angelman7/WRO-Binaries/jetson/scripts/images/img_0.png

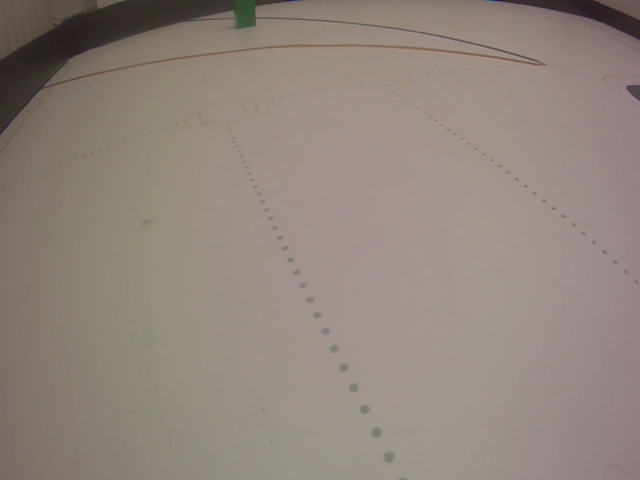
jetson/scripts/images/img_0.png
