angelman7/WRO-Binaries/jetson/scripts/images/img_1.png

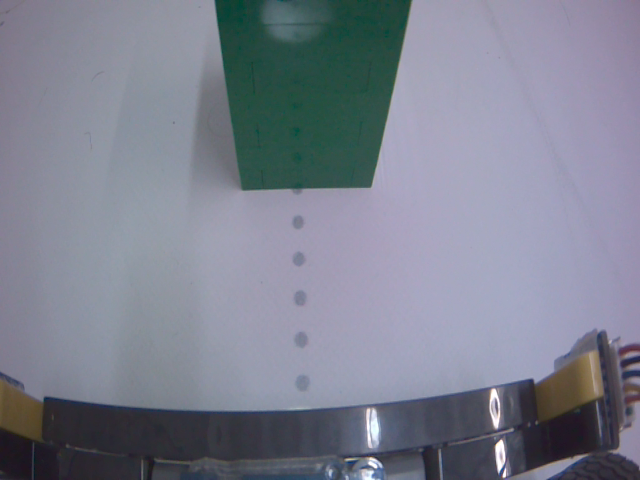
jetson/scripts/images/img_1.png
