angelman7/WRO-Binaries/jetson/scripts/images/img_2.png

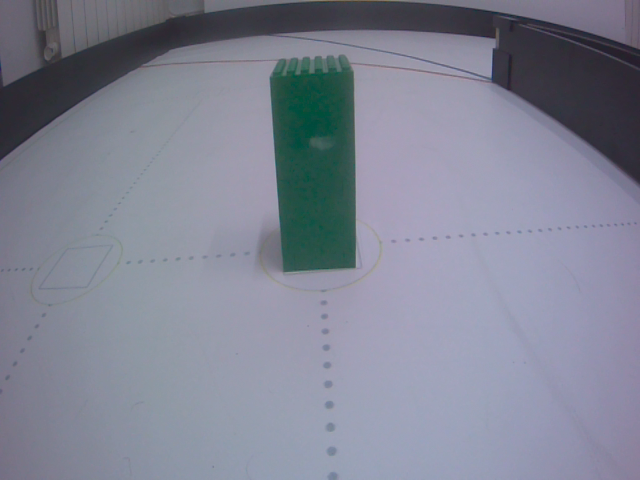
jetson/scripts/images/img_2.png
