angelman7/WRO-Binaries/jetson/scripts/images/img_7.png

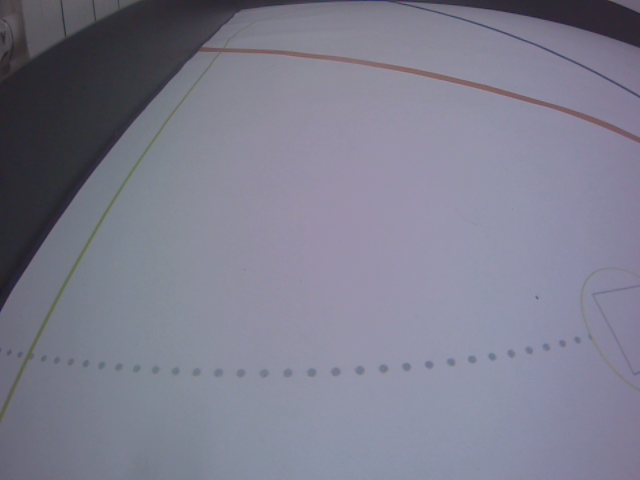
jetson/scripts/images/img_7.png
