angelman7/WRO-Binaries/jetson/scripts/images/img_9.png

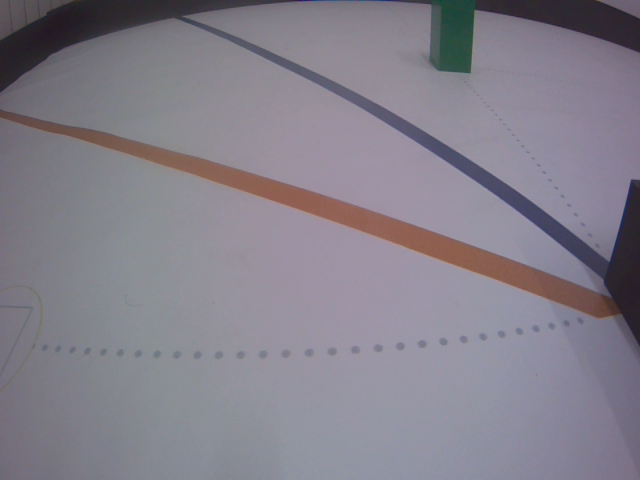
jetson/scripts/images/img_9.png
