angelman7/WRO-Binaries/jetson/scripts/images/img_11.png

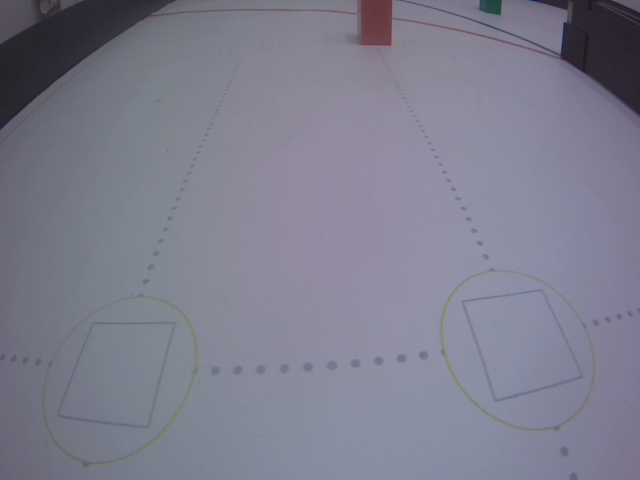
jetson/scripts/images/img_11.png
