angelman7/WRO-Binaries/jetson/scripts/images/img_13.png

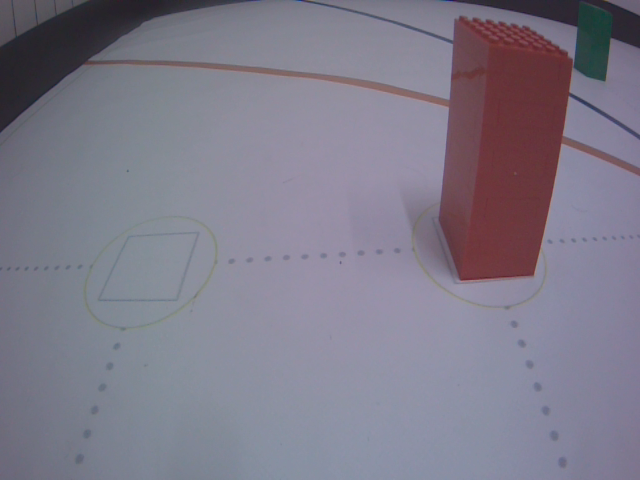
jetson/scripts/images/img_13.png
