angelman7/WRO-Binaries/jetson/scripts/images/img_15.png

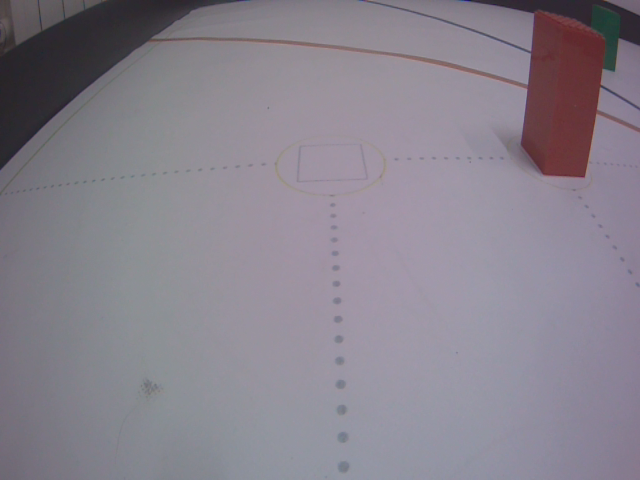
jetson/scripts/images/img_15.png
