angelman7/WRO-Binaries/schemes/Buttons.png

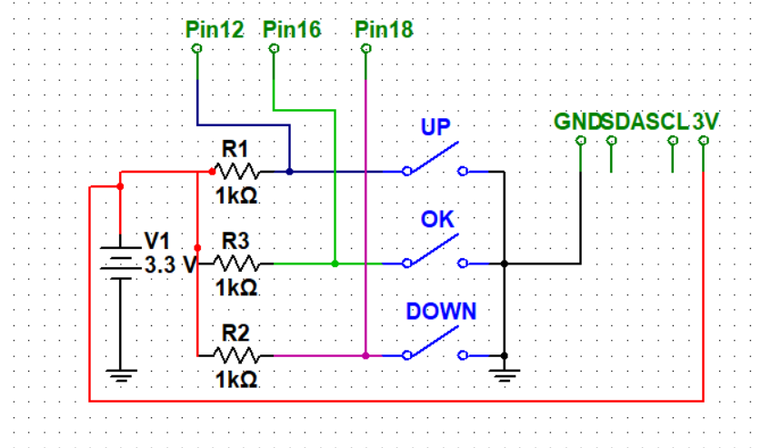
schemes/Buttons.png
