angelman7/WRO-Binaries/schemes/Power Distribution.png

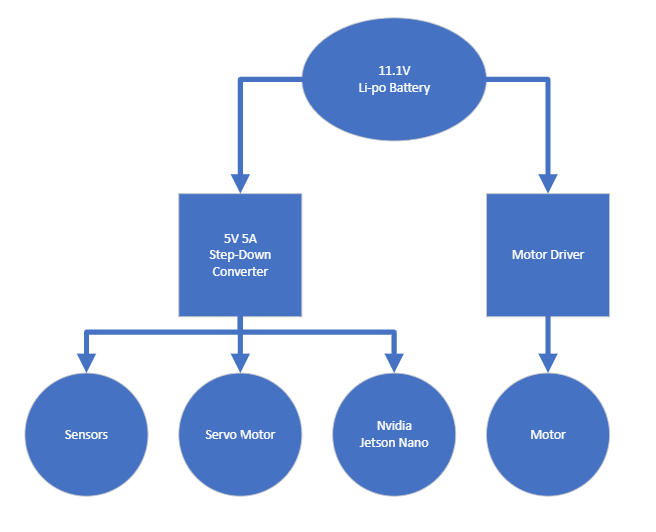
schemes/Power Distribution.png
