angelman7/WRO-Binaries/t-photos/56FD1CE0-8E3A-4A1B-88EE-9F9176FD94FB.jpeg

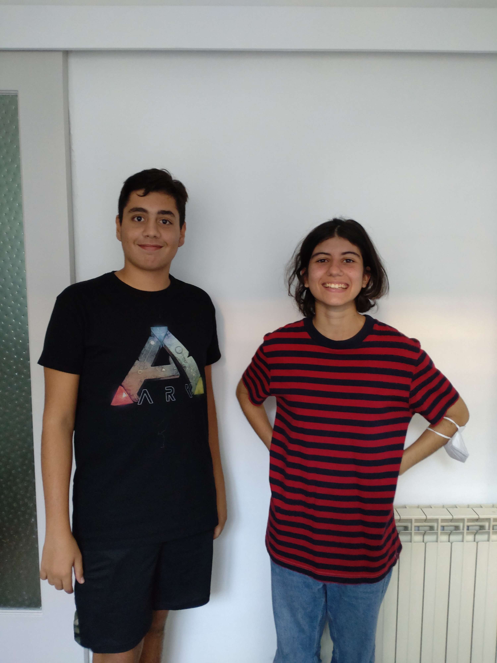
t-photos/56FD1CE0-8E3A-4A1B-88EE-9F9176FD94FB.jpeg
