angelman7/WRO-Binaries/t-photos/70BEBE67-610A-4704-82E0-13B6A6F9C980.jpeg

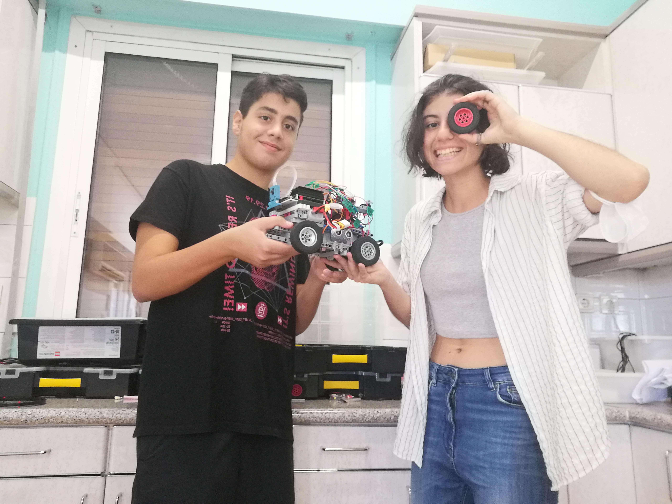
t-photos/70BEBE67-610A-4704-82E0-13B6A6F9C980.jpeg
