angelman7/WRO-Binaries/v-photos/img_back.jpg

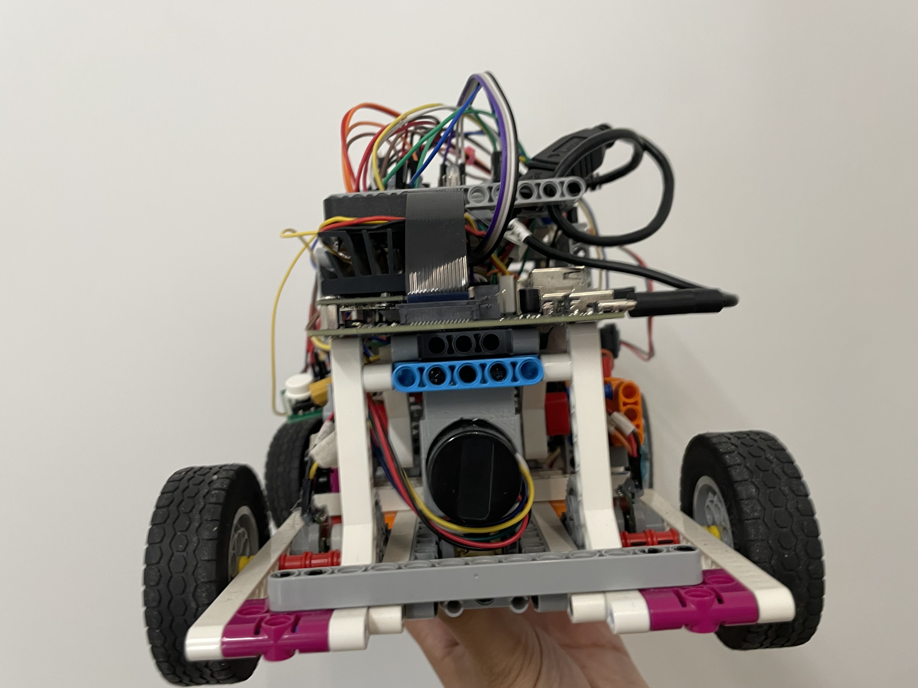
v-photos/img_back.jpg
