angelman7/WRO-Binaries/v-photos/img_front.jpg

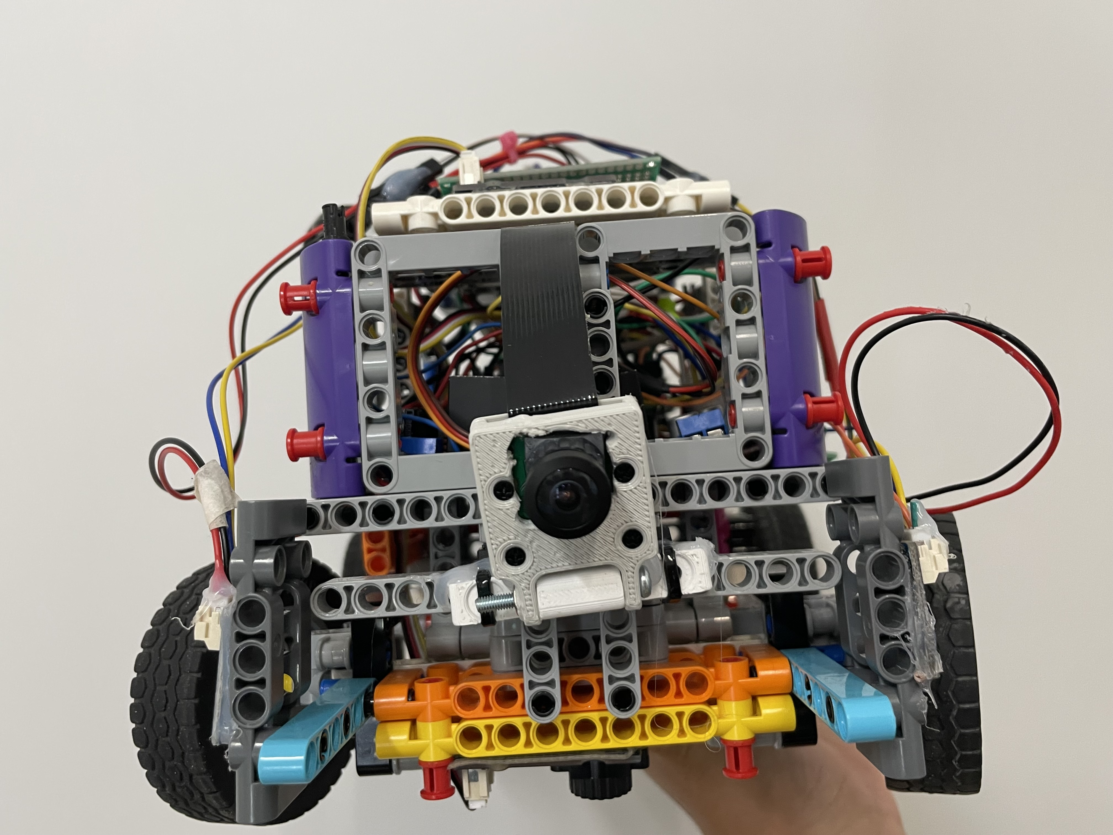
v-photos/img_front.jpg
