angelman7/WRO-Binaries/v-photos/img_left.jpg

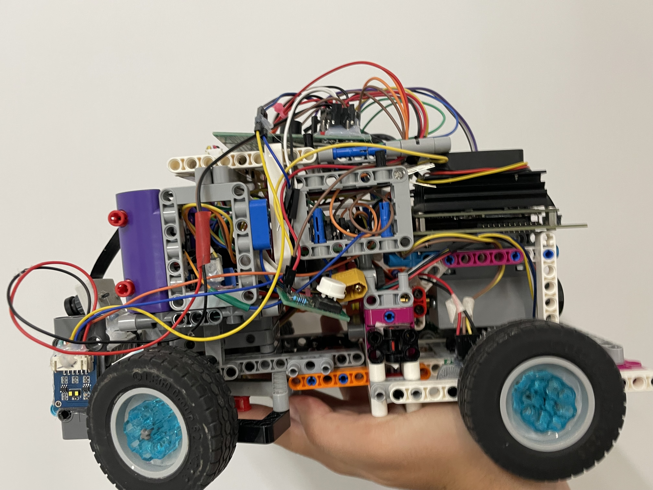
v-photos/img_left.jpg
