angelman7/WRO-Binaries/v-photos/img_right.jpg

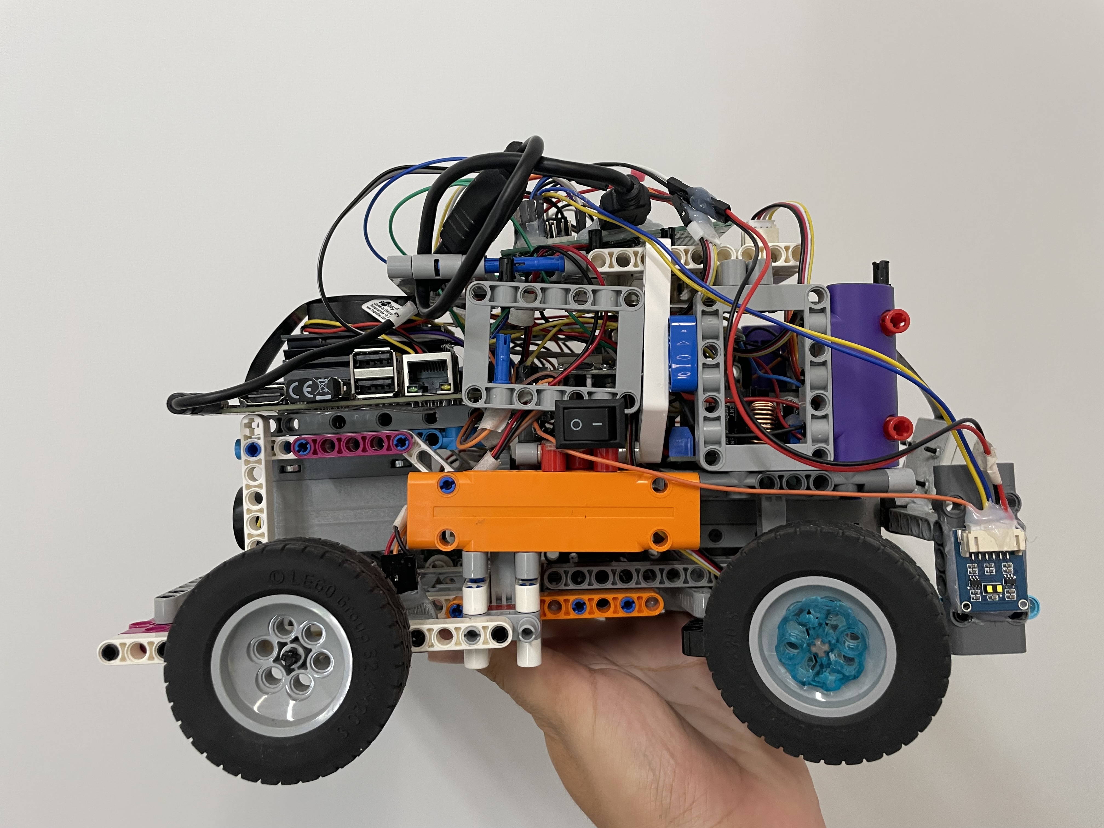
v-photos/img_right.jpg
