angelman7/WRO-Binaries/jetson/scripts/modules/grove_i2c_bus.py

# This is the library for Grove Base Hat which used to connect grove sensors for raspberry pi.
# We use python module smbus2 instead of smbus.
#
'''
## License

The MIT License (MIT)

Grove Base Hat for the Raspberry Pi, used to connect grove sensors.
Copyright (C) 2018  Seeed Technology Co.,Ltd. 

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
THE SOFTWARE IS PROVIDED "AS IS", WITHOUT WARRANTY OF ANY KIND, EXPRESS OR
IMPLIED, INCLUDING BUT NOT LIMITED TO THE WARRANTIES OF MERCHANTABILITY,
FITNESS FOR A PARTICULAR PURPOSE AND NONINFRINGEMENT. IN NO EVENT SHALL THE
AUTHORS OR COPYRIGHT HOLDERS BE LIABLE FOR ANY CLAIM, DAMAGES OR OTHER
LIABILITY, WHETHER IN AN ACTION OF CONTRACT, TORT OR OTHERWISE, ARISING FROM,
OUT OF OR IN CONNECTION WITH THE SOFTWARE OR THE USE OR OTHER DEALINGS IN
THE SOFTWARE.
'''
import smbus
# from smbus import i2c_msg
class Bus:
    instance = None
    MRAA_I2C = 0

    def __init__(self, bus=None):
        if bus is None:
            try:
                import RPi.GPIO as GPIO
                # use the bus that matches your raspi version
                rev = GPIO.RPI_REVISION
            except:
                rev = 3
            if rev == 2 or rev == 3:
                bus = 1  # for Pi 2+
            else:
                bus = 0
        if not Bus.instance:
            Bus.instance = smbus.SMBus(bus)
        self.bus = bus
        # self.msg = i2c_msg
    def __getattr__(self, name):
        return getattr(self.instance, name)
